BrettHallen/Sura_PC8000/Documentation/Sura_PC8000_-5VDC.png

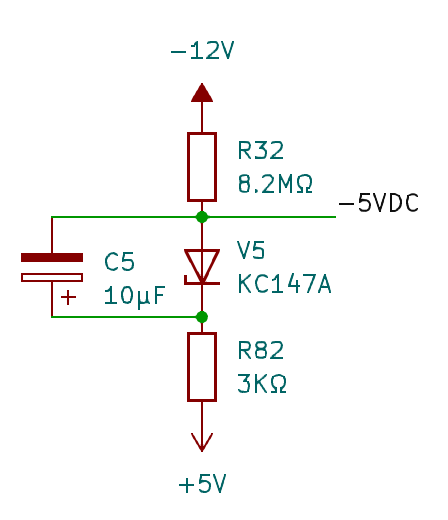
Documentation/Sura_PC8000_-5VDC.png
