BrettHallen/Sura_PC8000/HDMI_Video_Adaptor_EN/Sura_RU.png

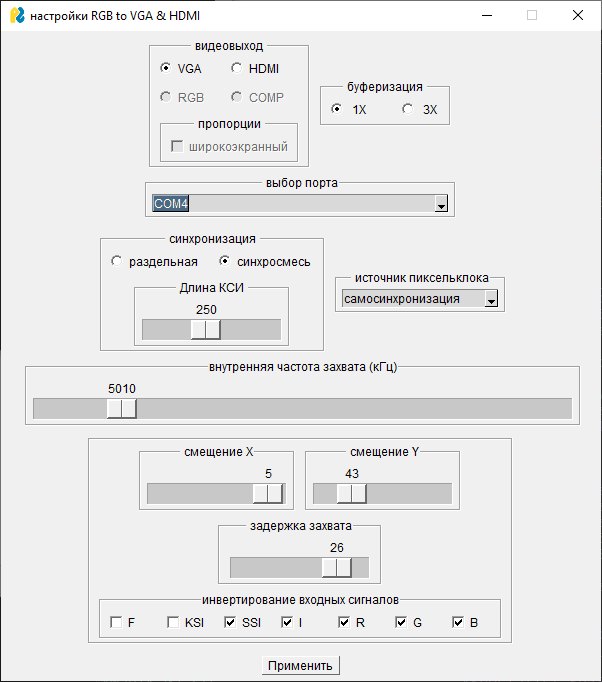
HDMI_Video_Adaptor_EN/Sura_RU.png
