BrettHallen/Sura_PC8000/Images/Sura_PC8000_Keyboard_PCB.jpeg

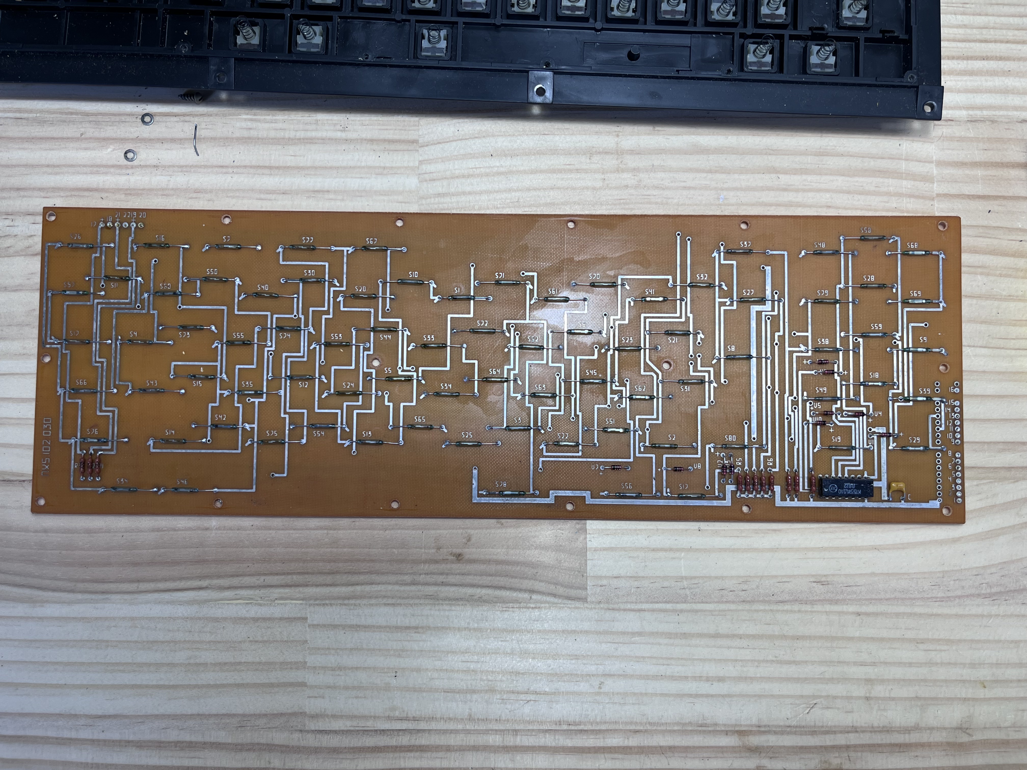
Images/Sura_PC8000_Keyboard_PCB.jpeg
