BrettHallen/Sura_PC8000/Images/Sura_PC8000_Keyboard_К155ИД10.jpeg

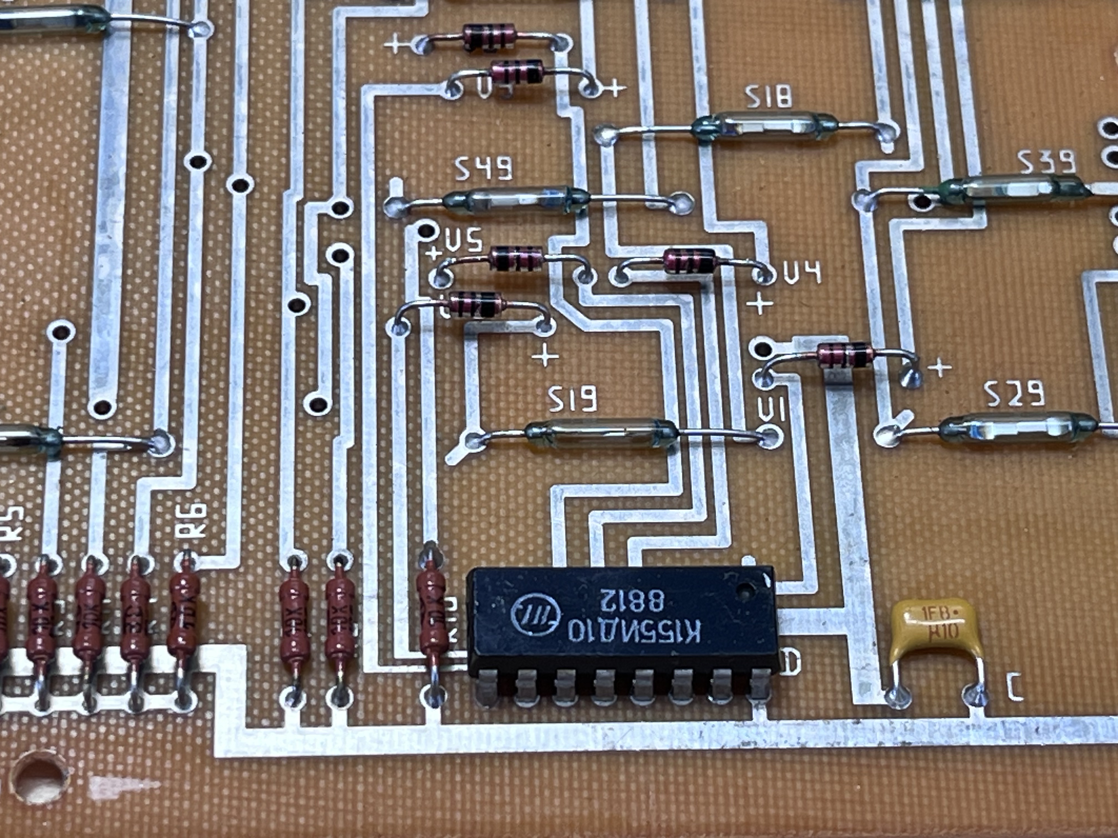
Images/Sura_PC8000_Keyboard_К155ИД10.jpeg
