BrettHallen/Sura_PC8000/Images/Sura_PC8000_Keycap.jpeg

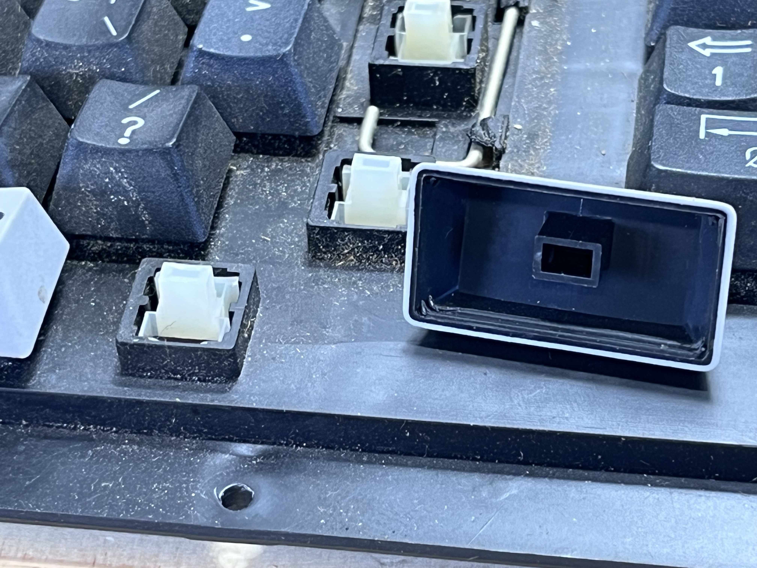
Images/Sura_PC8000_Keycap.jpeg
