BrettHallen/Sura_PC8000/Images/Sura_PC8000_Keyswitch_Orientation.jpeg

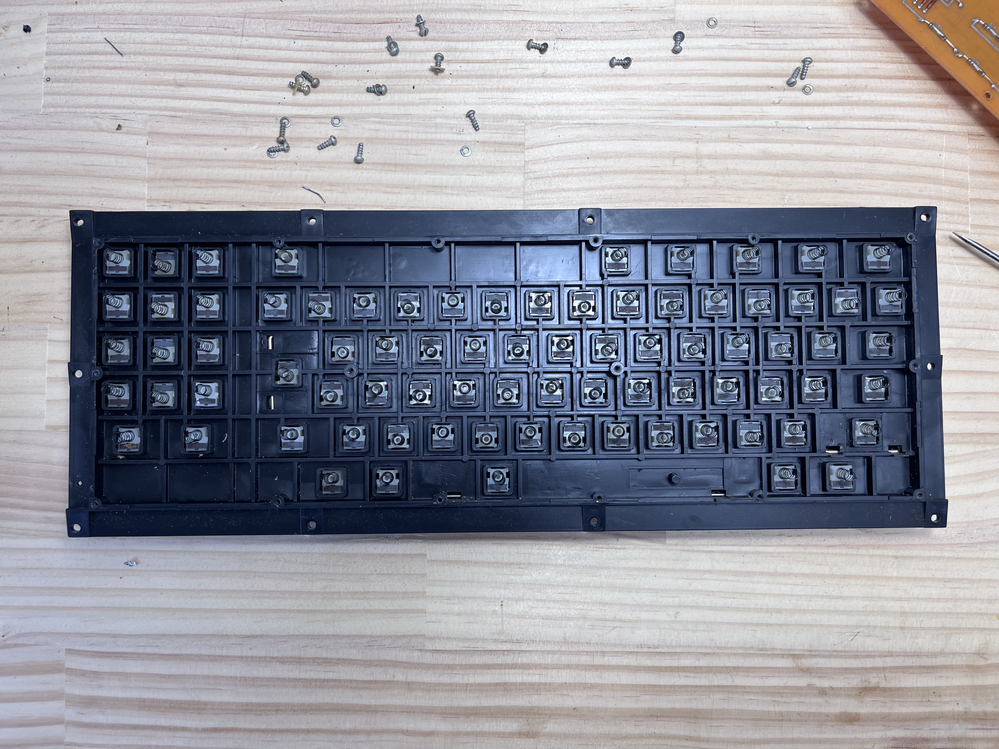
Images/Sura_PC8000_Keyswitch_Orientation.jpeg
