BrettHallen/Sura_PC8000/Images/Sura_PC8000_Original.png

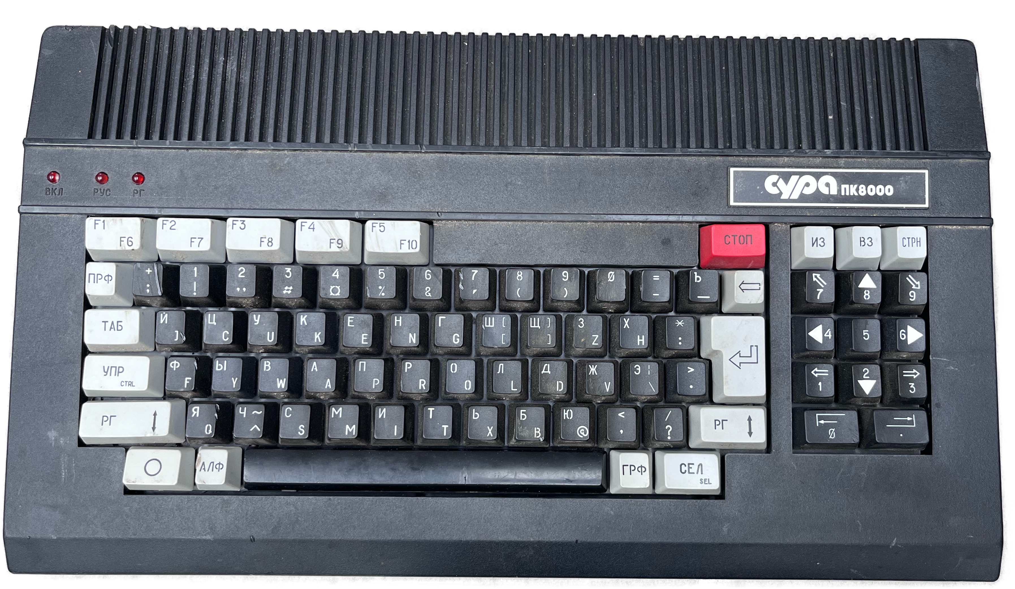
Images/Sura_PC8000_Original.png
