BrettHallen/Sura_PC8000/Images/Sura_PC8000_PSU4.jpeg

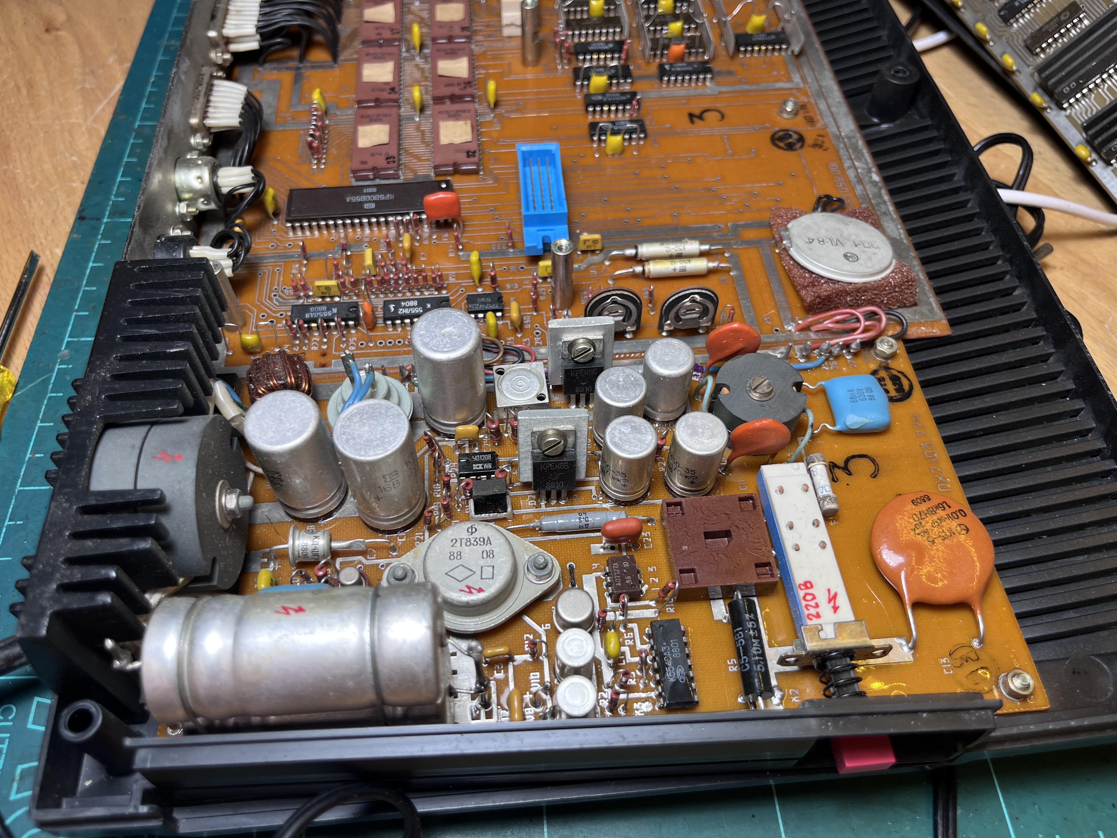
Images/Sura_PC8000_PSU4.jpeg
