BrettHallen/Sura_PC8000/Images/Sura_PC8000_Reed_Switch.jpeg

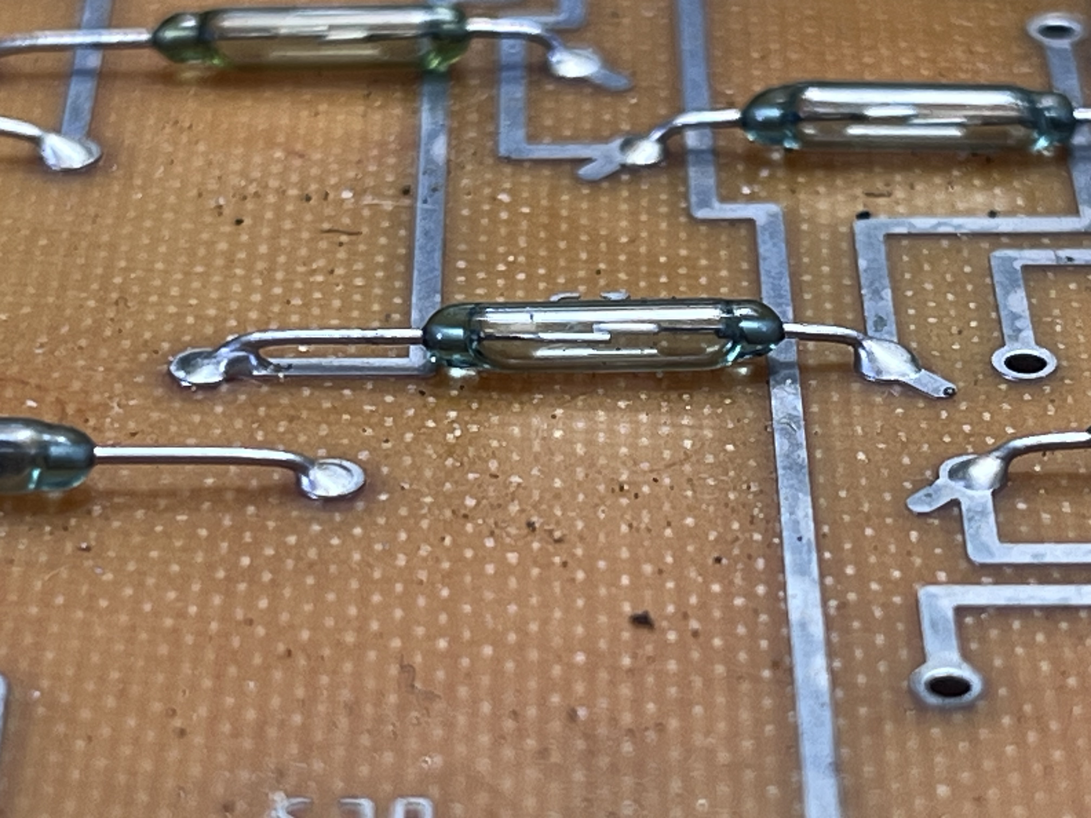
Images/Sura_PC8000_Reed_Switch.jpeg
