BrettHallen/Sura_PC8000/Images/Sura_PC8000_Keyboard_Wiring.jpeg

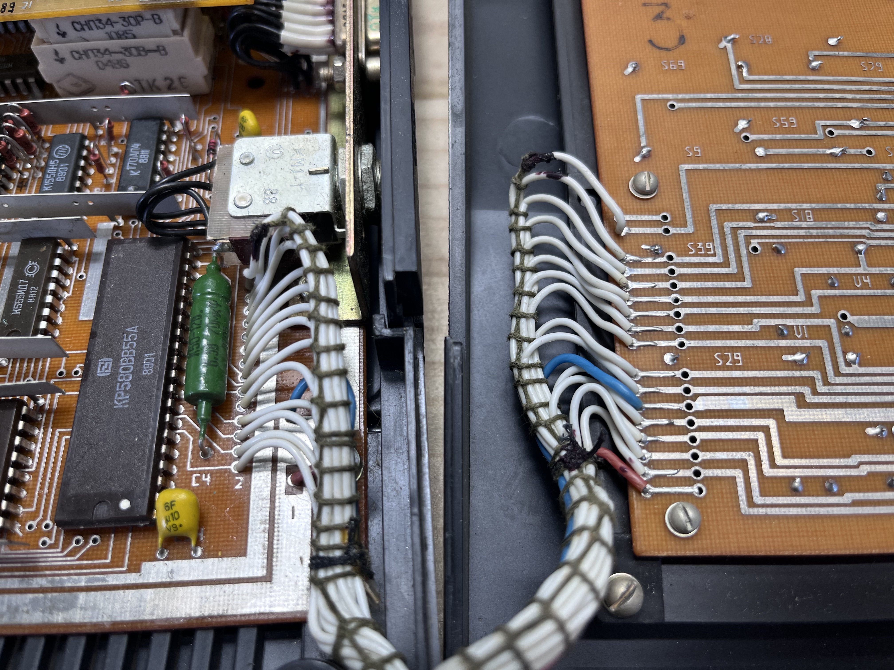
Images/Sura_PC8000_Keyboard_Wiring.jpeg
