BrettHallen/Sura_PC8000/Images/Sura_PC8000_LED_Indicator_Wiring.jpeg

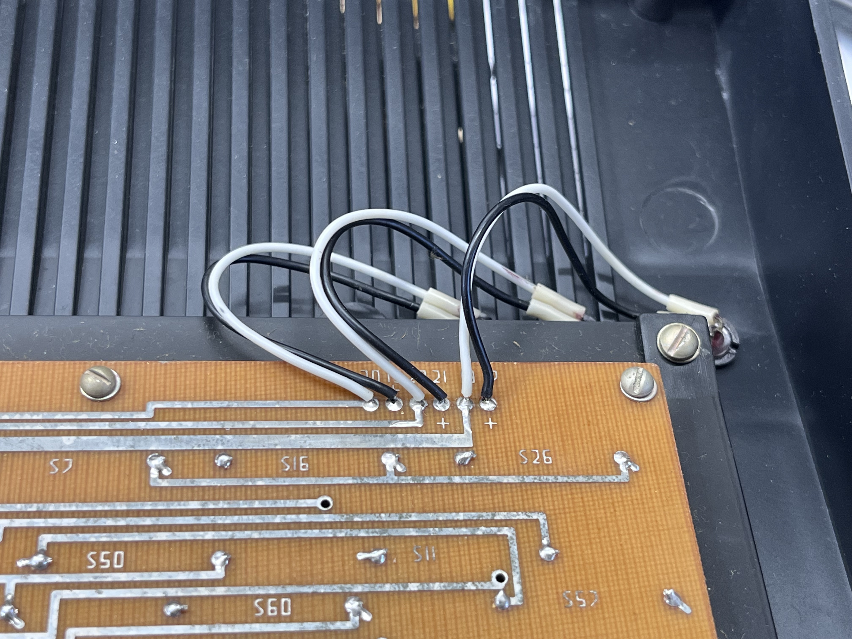
Images/Sura_PC8000_LED_Indicator_Wiring.jpeg
